YeetTheAnson/WhoopDock-6-Pro/cartScreenshots/JLCCart.png

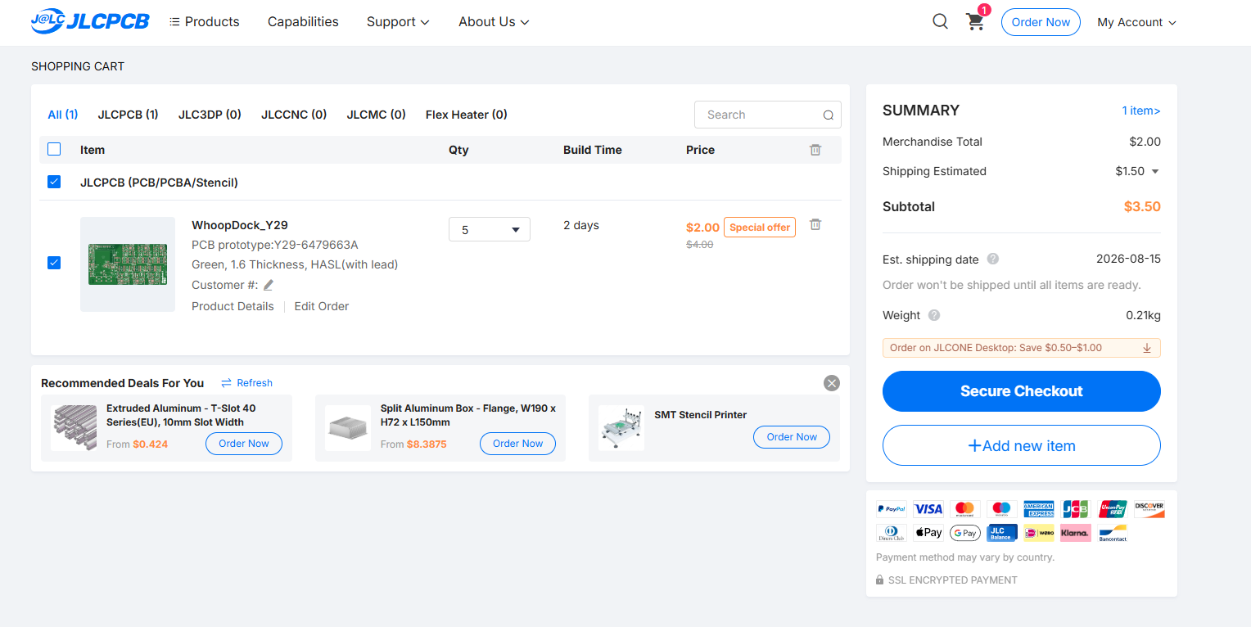
cartScreenshots/JLCCart.png
