YeetTheAnson/WhoopDock-6-Pro/cartScreenshots/JLCCheckout1.jpeg

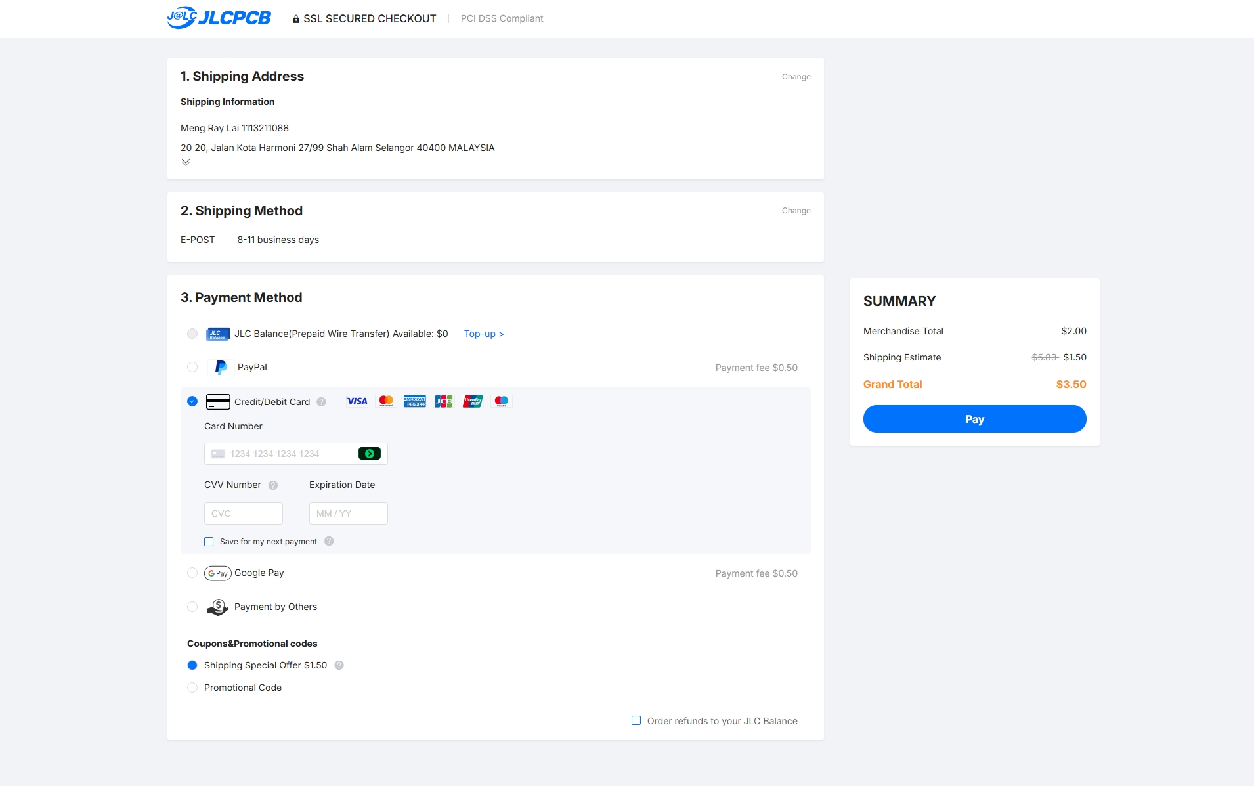
cartScreenshots/JLCCheckout1.jpeg
