YeetTheAnson/WhoopDock-6-Pro/cartScreenshots/JLCCheckout2.png

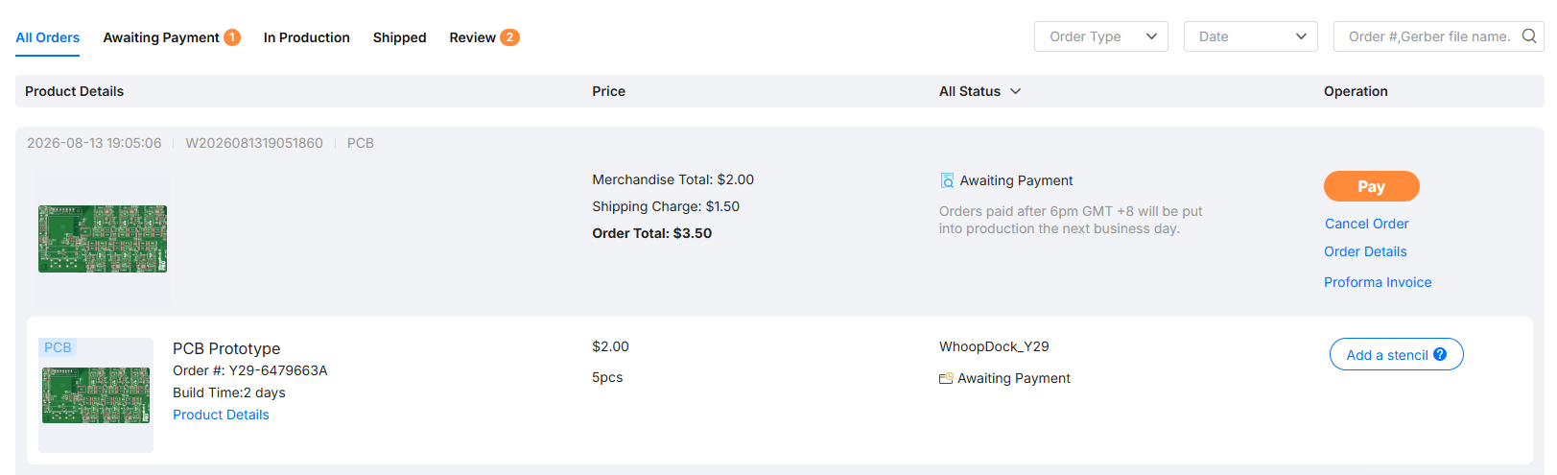
cartScreenshots/JLCCheckout2.png
