YeetTheAnson/WhoopDock-6-Pro/cartScreenshots/JLCShipping.png

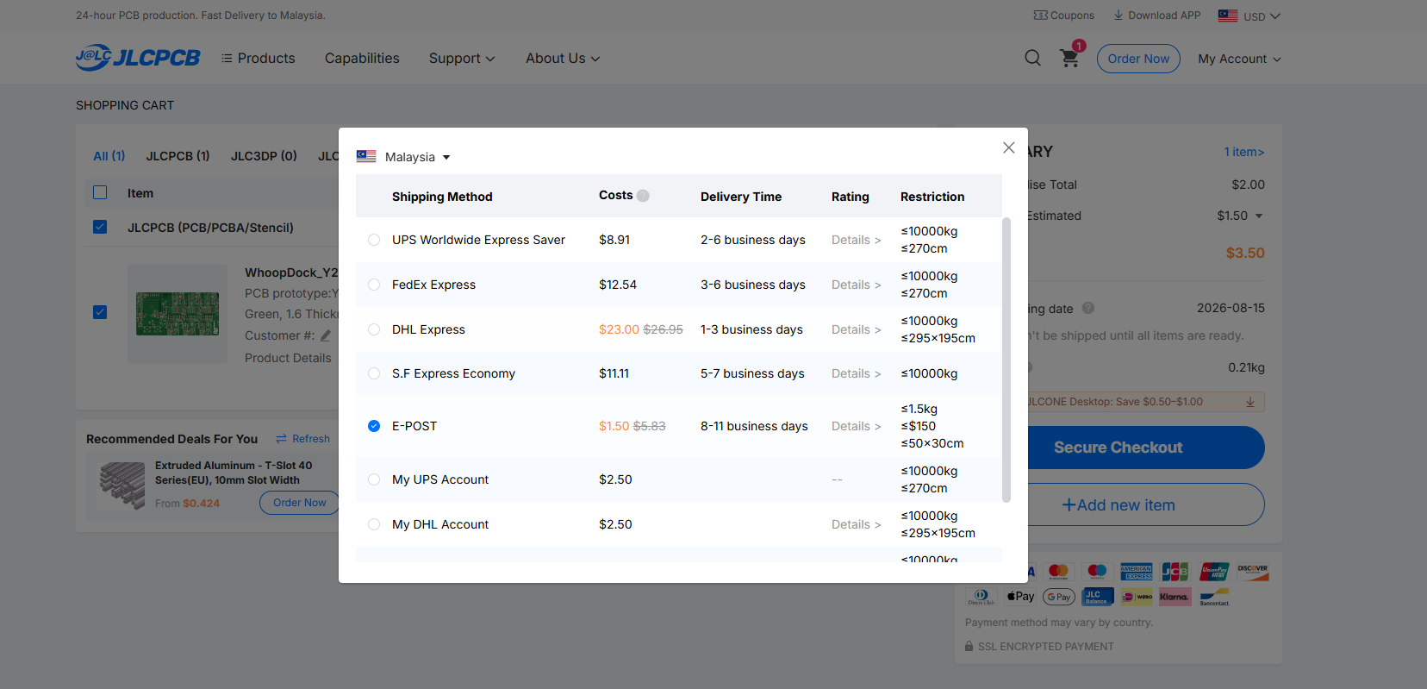
cartScreenshots/JLCShipping.png
