YeetTheAnson/WhoopDock-6-Pro/cartScreenshots/shopee.jpeg

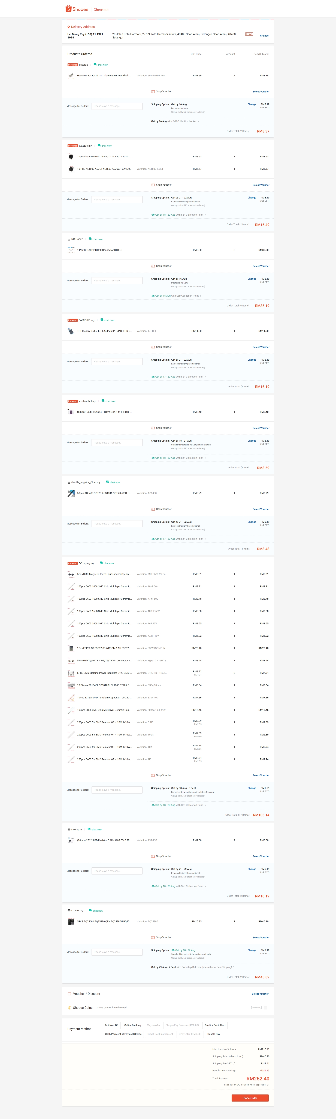
cartScreenshots/shopee.jpeg
